ieb/nmea2000/sumulateTransducersWithDAC/ShiftOutputVoltage.asc

R1: res; 10k
R2: res; 10K
R3: res; 1K
R4: res; 10k
R5: res; 10K
U1: LT1413
V1: voltage; SINE(1.5 1.5 10)
V2: voltage; 8v
Named nets: 0
.tran 1000m startup
